Bastelschlumpf/WireWizard/src/WireWizard/Motors.h

/*
   Copyright (C) 2024 SFini

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
   You should have received a copy of the GNU General Public License
   along with this program.  If not, see <http://www.gnu.org/licenses/>.
*/
#pragma once

/**
  * @file Motors.h
  * 
  * Stepper Interface
  */

class Motors
{
private:
  bool enabled;
  bool enabledOnIdle;
  long currPosX;
  long currPosY;
  long currPosZ;
  long doStepsX;
  long doStepsY;
  long doStepsZ;
  long delayUs;
  long beepMs;

private:
  static void motorTask(void *parg);

private:
  void serialOut     (byte value);
  void setEnableBit  (byte &value, short enableBit, bool enable);
  void setBeepBit    (byte &value, short beepBit, TickType_t startTickCount, long &beepMs);
  void setStepperBit (byte &value, short dirBit, short stepBit, long &doSteps, long &pos);

public:
  Motors();

  void begin();

  void reset();
  void resetSteps();

  void enable(bool en);
  bool isEnabled()           { return enabled;       }

  bool isIdle()              { return isIdleX() && isIdleY() && isIdleZ(); }
  bool isIdleX()             { return doStepsX == 0; }
  bool isIdleY()             { return doStepsY == 0; }
  bool isIdleZ()             { return doStepsZ == 0; }
  bool isIdleBeep()          { return beepMs   == 0; }

  void enableOnIdle(bool en) { enabledOnIdle = en;   }

  long getPosX()             { return currPosX;      }
  long getPosY()             { return currPosY;      }
  long getPosZ()             { return currPosZ;      }
  void stepX(int steps)      { if (enabled) doStepsX += steps; }
  void stepY(int steps)      { if (enabled) doStepsY += steps; }
  void stepZ(int steps)      { if (enabled) doStepsZ += steps; }

  void delay(int us)         { delayUs = us;         }

  void beep(int ms)          { beepMs = ms;          }
};
